joanperelopez/RF-Common-Mode-choque/IMAGES/WhatsApp Image 2025-04-26 at 18.15.17-2.jpeg

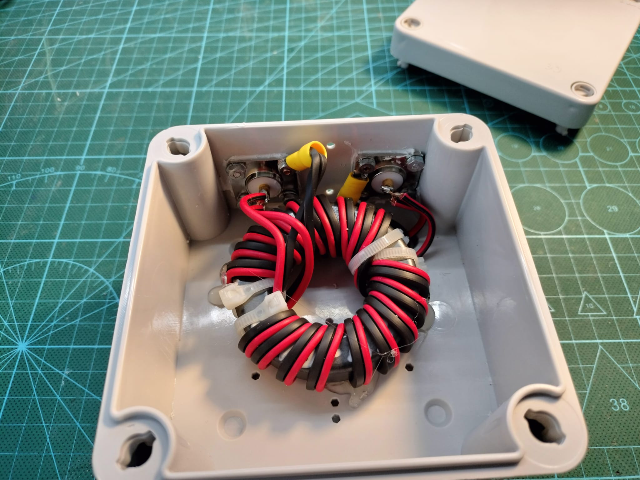
IMAGES/WhatsApp Image 2025-04-26 at 18.15.17-2.jpeg
